ptBauke1/mini_agv/projeto_mecanico/base.SLDPRT

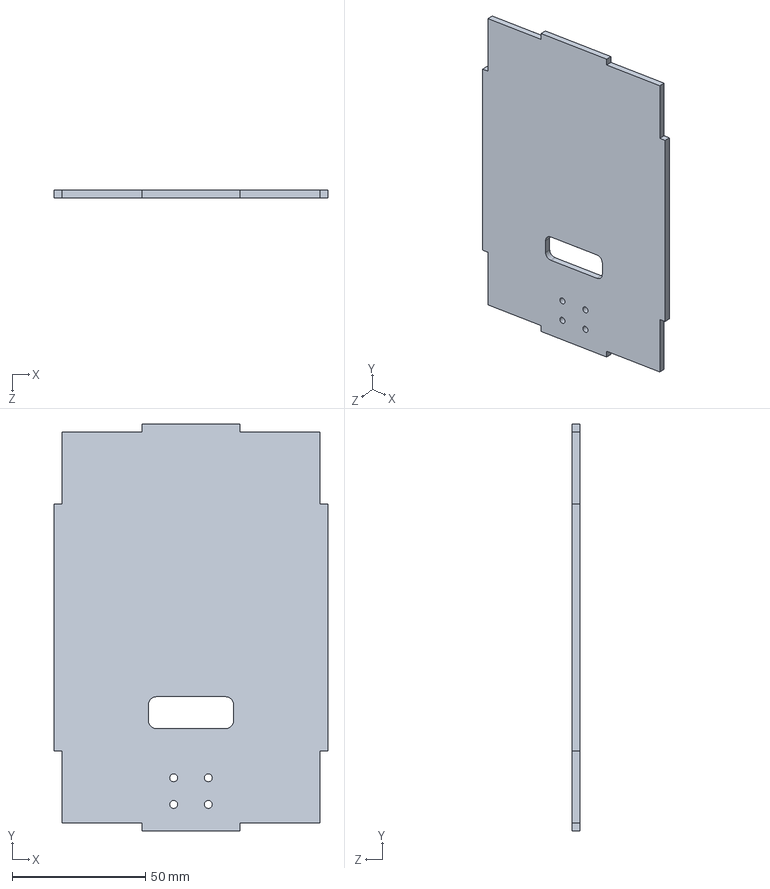
[picture p27: CAD file, 2025-11-27]
projeto_mecanico/base.SLDPRT
103.0 x 153.0 x 3.00 mm
